ErnestoOjeda/gps-tracker/images/wander-v1.1 back.png

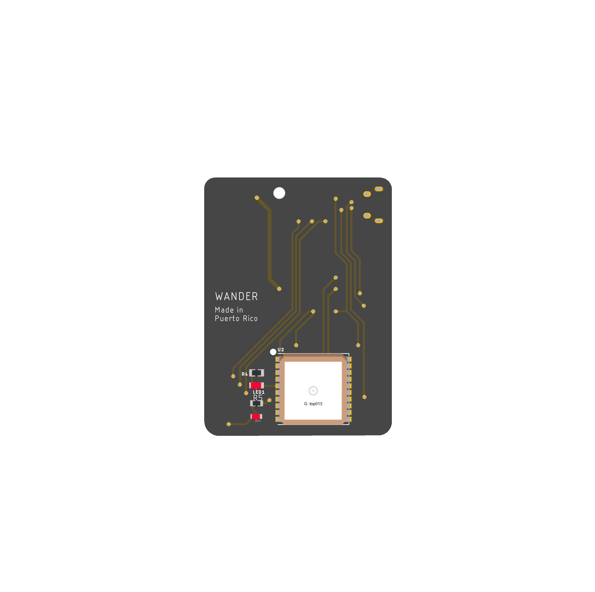
images/wander-v1.1 back.png
